Elecrow-RD/All-in-one-Starter-Kit-for-Pico-2/Eagle_SCH&PCB/V1.3/V1.3.png

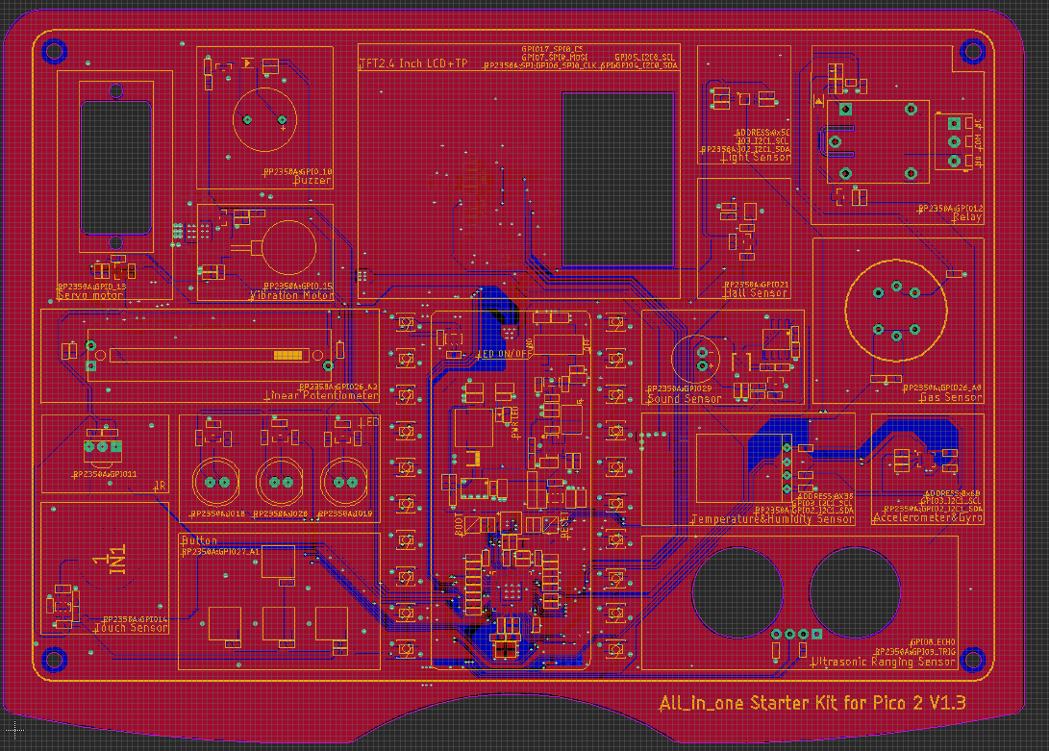
Eagle_SCH&PCB/V1.3/V1.3.png
